jjwbruijn/POCSAG_FLEX_Modem/ESP32-firmware/include/rfconfig.h

static const uint8_t PROGMEM rf4463TXsetup0[] = {0x23, 0x07, 0x02, 0x81, 0x00, 0x01, 0xc9, 0xc3, 0x80, 0x08, 0x13, 0x00, 0x14, 0x00, 0x00, 0x00, 0x00, 0x00, 0x06, 0x11, 0x00, 0x02, 0x00, 0x52, 0x01, 0x05, 0x11, 0x00, 0x01, 0x03, 0x20, 0x06, 0x11, 0x01, 0x02, 0x00, 0x01, 0xe2, 0x08, 0x11, 0x02, 0x04, 0x00, 0x00, 0x00, 0x00, 0x00, 0x0d, 0x11, 0x10, 0x09, 0x00, 0x00, 0x14, 0x00, 0x0f, 0x11, 0x00, 0x00, 0x00, 0x00, 0x0a, 0x11, 0x11, 0x06, 0x00, 0x80, 0x00, 0x00, 0x00, 0x00, 0x00, 0x10, 0x11, 0x12, 0x0c, 0x00, 0x00, 0x00, 0x30, 0xff, 0xff, 0x00, 0x22, 0x80, 0x00, 0x00, 0x00, 0x30, 0x10, 0x11, 0x12, 0x0c, 0x0c, 0x30, 0x00, 0x04, 0x10, 0x80, 0x00, 0x00, 0x00, 0x00, 0x00, 0x00, 0x00, 0x10, 0x11, 0x12, 0x0c, 0x18, 0x00, 0x00, 0x00, 0x00, 0x00, 0x00, 0x00, 0x00, 0x00, 0x00, 0x00, 0x00, 0x10, 0x11, 0x12, 0x0c, 0x24, 0x00, 0x00, 0x00, 0x00, 0x00, 0x00, 0x00, 0x00, 0x00, 0x00, 0x00, 0x00, 0x09, 0x11, 0x12, 0x05, 0x30, 0x00, 0x00, 0x00, 0x00, 0x00, 0x08, 0x11, 0x12, 0x04, 0x36, 0x00, 0x00, 0x00, 0x00, 0x10, 0x11, 0x20, 0x0c, 0x00, 0x05, 0x00, 0x07, 0x01, 0xe8, 0x48, 0x05, 0xc9, 0xc3, 0x80, 0x00, 0x03, 0x05, 0x11, 0x20, 0x01, 0x0c, 0xd7, 0x10, 0x11, 0x20, 0x0c, 0x18, 0x05, 0x00, 0x08, 0x02, 0x80, 0x00, 0xb0, 0x20, 0x0c, 0xe8, 0x00, 0x96, 0x10, 0x11, 0x20, 0x0c, 0x24, 0x03, 0x69, 0xd0, 0x01, 0x23, 0x02, 0x02, 0x00, 0x00, 0x12, 0x80, 0x52, 0x07, 0x11, 0x20, 0x03, 0x30, 0x04, 0x05, 0xa0, 0x05, 0x11, 0x20, 0x01, 0x35, 0xe0, 0x10, 0x11, 0x20, 0x0c, 0x38, 0x11, 0x21, 0x21, 0x00, 0x1a, 0x3f, 0xfb,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
#define RX_FREQS 10
#define TX_FREQS 13
